GlowPon3/spool-helpter/20240527_203010.jpg

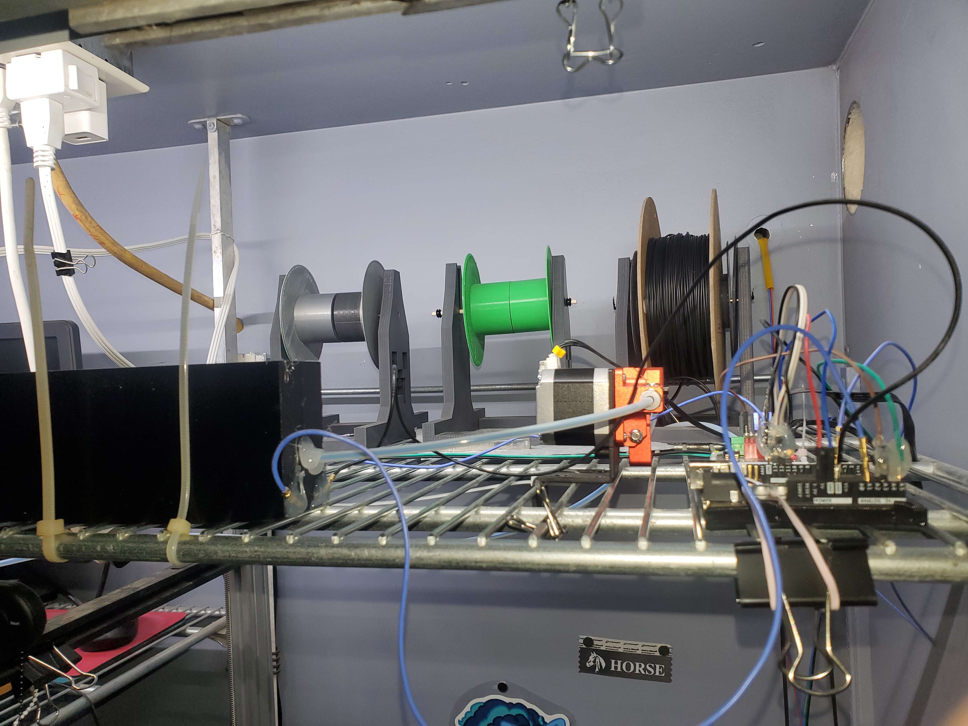
20240527_203010.jpg
