GlowPon3/spool-helpter/20240527_203032.jpg

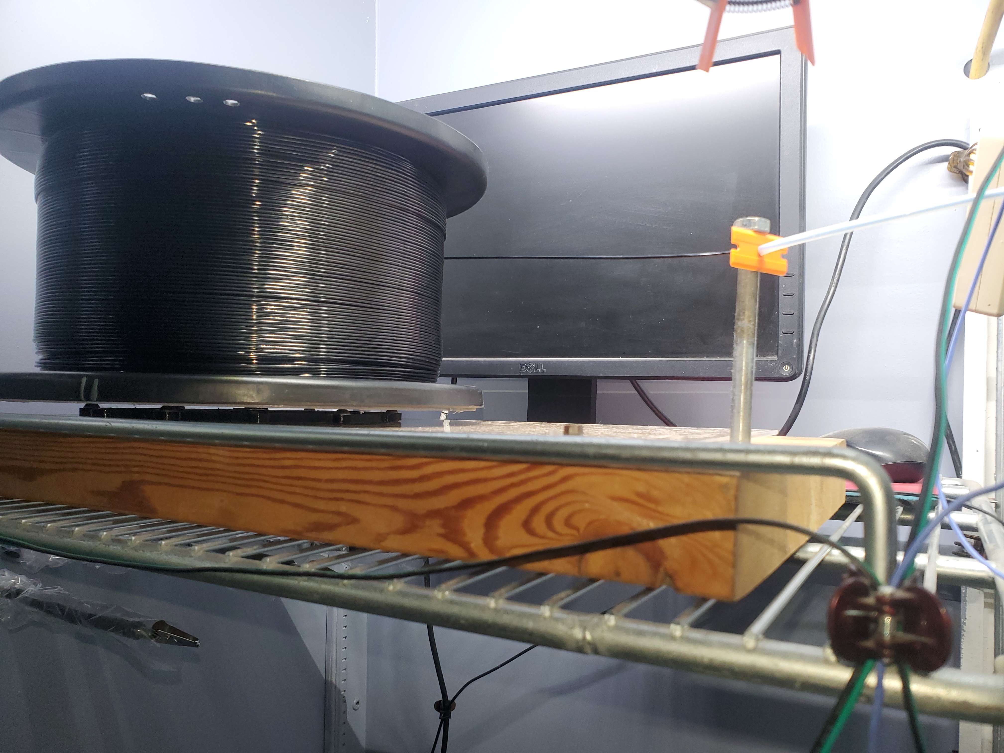
20240527_203032.jpg
